vad7/CO2_HUB_ESP32-S3/Build/enclosure/TDisplayS3_lid_wall.stl

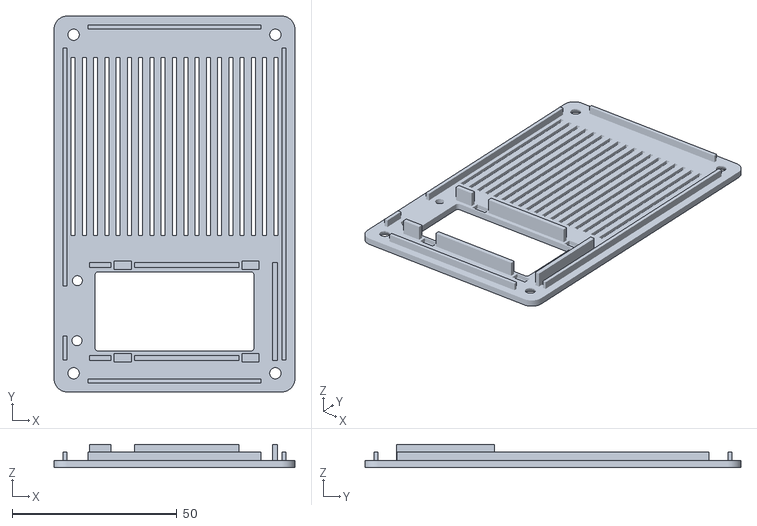
[picture p16: CAD file, 2026-10-08]
Build/enclosure/TDisplayS3_lid_wall.stl
73.0 x 114.0 x 7.10
