vad7/CO2_HUB_ESP32-S3/Build/enclosure/TDisplayS3_clips_x4.stl

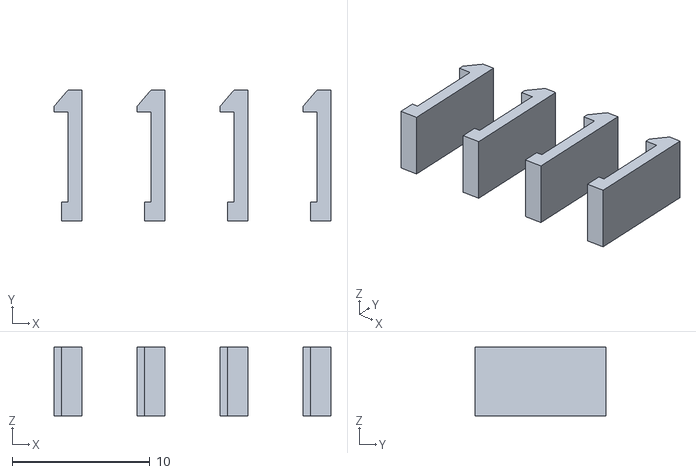
[picture p17: CAD file, 2026-10-08]
Build/enclosure/TDisplayS3_clips_x4.stl
20.1 x 9.56 x 5.00
