vad7/CO2_HUB_ESP32-S3/Build/enclosure/Test_slots.stl

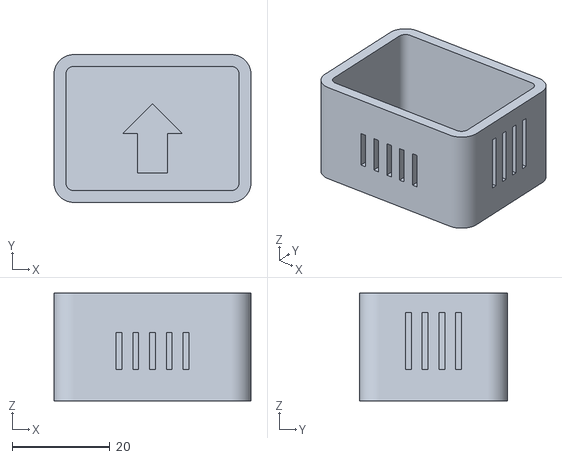
[picture p18: CAD file, 2026-10-08]
Build/enclosure/Test_slots.stl
40.2 x 30.2 x 22.0
