vad7/CO2_HUB_ESP32-S3/Build/enclosure/ES3C28P_preview.png

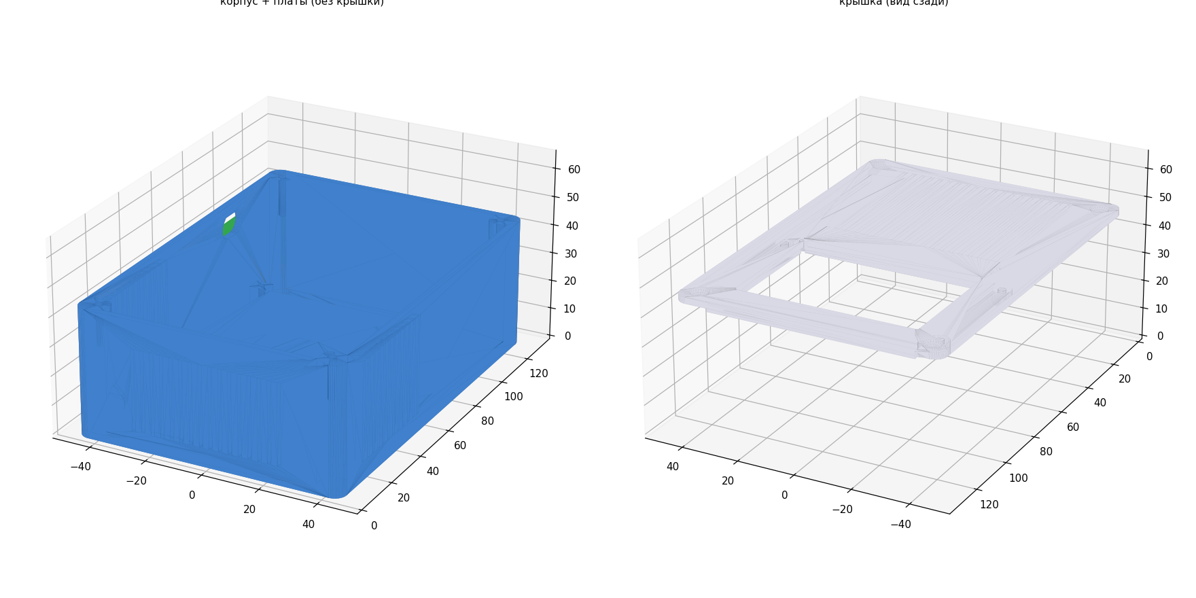
Build/enclosure/ES3C28P_preview.png
