vad7/CO2_HUB_ESP32-S3/Build/enclosure/TDisplayS3_S8_preview.png

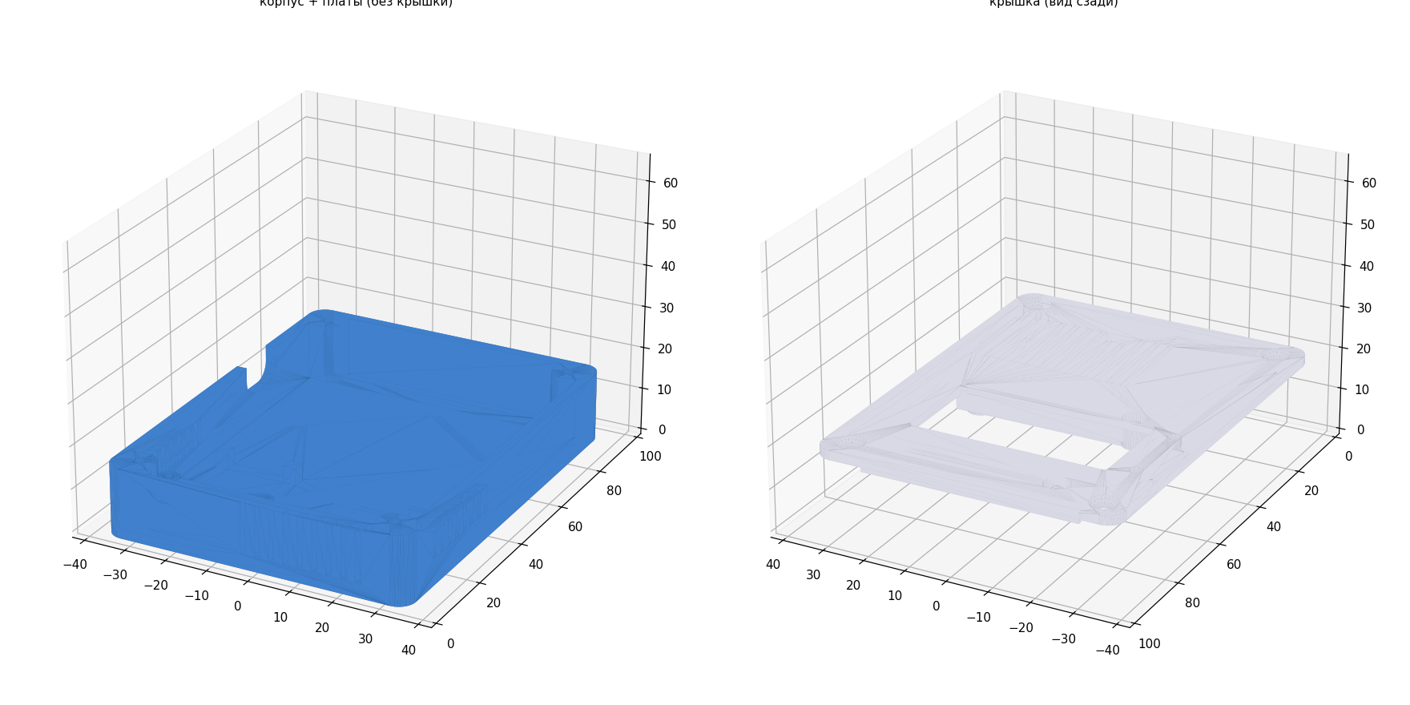
Build/enclosure/TDisplayS3_S8_preview.png
